jgottula/automaton/src/io/spi.c

/* automaton
 * (c) 2013 Justin Gottula
 * The source code of this project is distributed under the terms of the
 * simplified BSD license. See the LICENSE file for details.
 */


#include "io/spi.h"


static volatile bool spi_xfer_flag = false;


ISR(SPI_STC_vect) {
	spi_xfer_flag = true;
}


static void _spi_select(uint8_t slave){
	IO_WRITE(PORT(IO_SPI), IO_SPI_SS_ALL, IO_SPI_SS_ALL ^ slave);
}

static void _spi_deselect(void) {
	IO_WRITE(PORT(IO_SPI), IO_SPI_SS_ALL, IO_SPI_SS_ALL);
}


void spi_init(void) {
	/* all output except MISO; all high, plus pullups on MISO */
	IO_WRITE(PORT(IO_SPI), IO_SPI_ALL | IO_SPI_SS_ALL, IO_SPI_SS_ALL);
	IO_WRITE(DDR(IO_SPI), IO_SPI_ALL | IO_SPI_SS_ALL,
		(IO_SPI_ALL ^ IO_SPI_MISO) | IO_SPI_SS_ALL);
}


void spi_select(uint8_t slave, uint8_t settings) {
	SPCR = _BV(MSTR) | (settings & ~_BV(7));
	SPSR = ((settings & _BV(7)) ? _BV(SPI2X) : 0);
	
	/* clear out any existing state */
	(void)SPSR;
	(void)SPDR;
	
	_spi_select(slave);
}

void spi_deselect(void) {
	_spi_deselect();
}


uint8_t spi_xfer(uint8_t tx) {
	SPDR = tx;
	
	while (!(SPSR & _BV(SPIF)));
	return SPDR;
}


void spi_async_begin(uint8_t tx) {
	SPCR |= _BV(SPIE);
	
	spi_xfer_flag = false;
	SPDR = tx;
}

bool spi_async_end(uint8_t *rx) {
	if (spi_xfer_flag) {
		SPCR &= ~_BV(SPIE);
		
		*rx = SPDR;
		return true;
	} else {
		return false;
	}
}
